axtar/Nixie-Solar-Power-Flow-Monitor/Software/Firmware/Solar Monitor/include/main.h

// main.h

// Solar Monitor Firmware

// Copyright (C) 2024 highvoltglow
// Licensed under the MIT License

#pragma once

//- INCLUDES
#include <Arduino.h>
#include <Controller.hpp>

Controller controller;
