axtar/Nixie-Solar-Power-Flow-Monitor/Software/Firmware/Solar Monitor/include/FirmwareInfo.h

// FirmwareInfo.h

// Provides information about the firmware version

// Copyright (C) 2024 highvoltglow
// Licensed under the MIT License

#pragma once

//- VERSION
#define MAJOR_VERSION 0
#define MINOR_VERSION 1
#define REVISION 5
#define FW_STATUS "beta"
